DickSwart/smart-fish-tank/assits/images/fish-tank/IMG_0641.jpeg

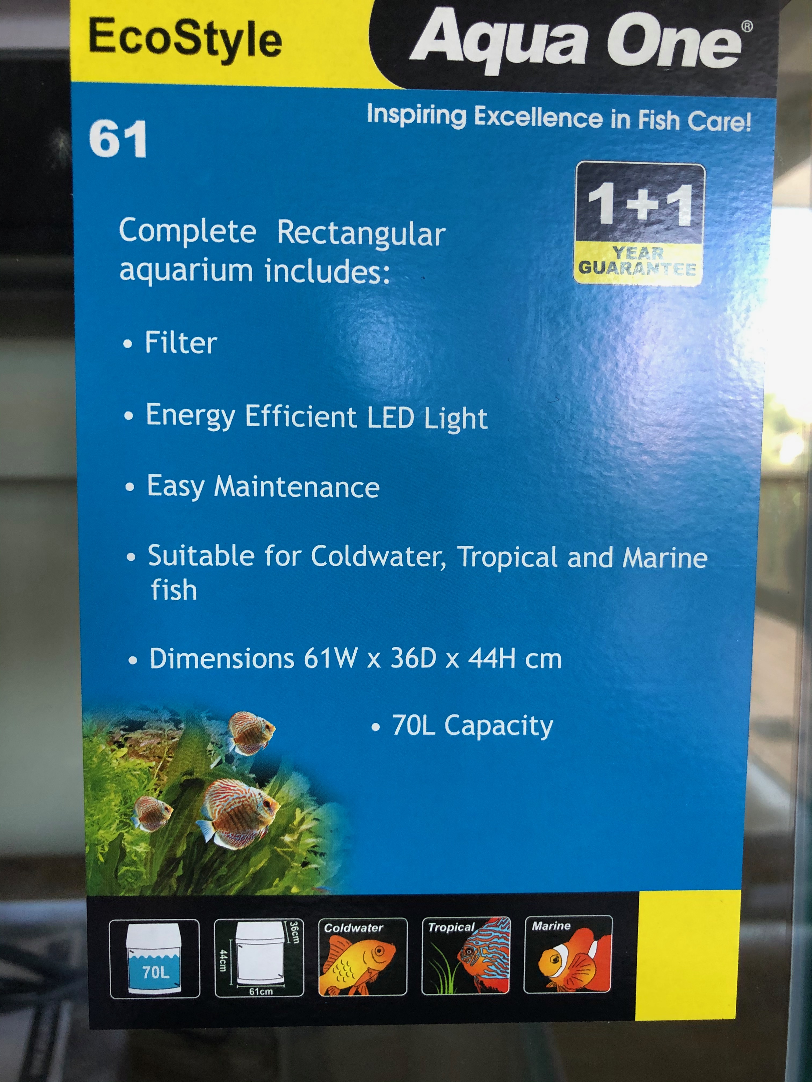
assits/images/fish-tank/IMG_0641.jpeg
