DickSwart/smart-fish-tank/assits/images/fish-tank/IMG_0642.jpeg

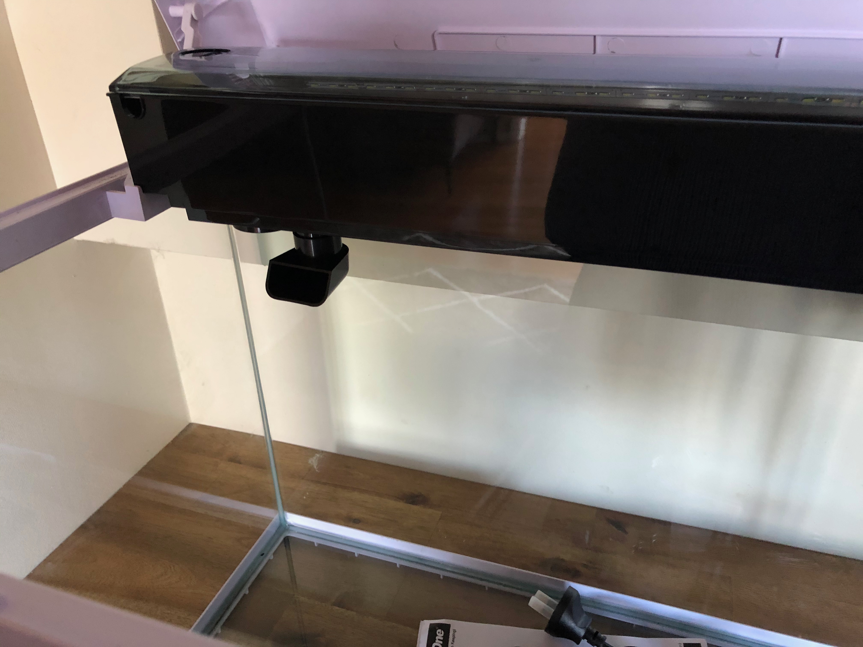
assits/images/fish-tank/IMG_0642.jpeg
