DickSwart/smart-fish-tank/assits/images/fish-tank/IMG_0643.jpeg

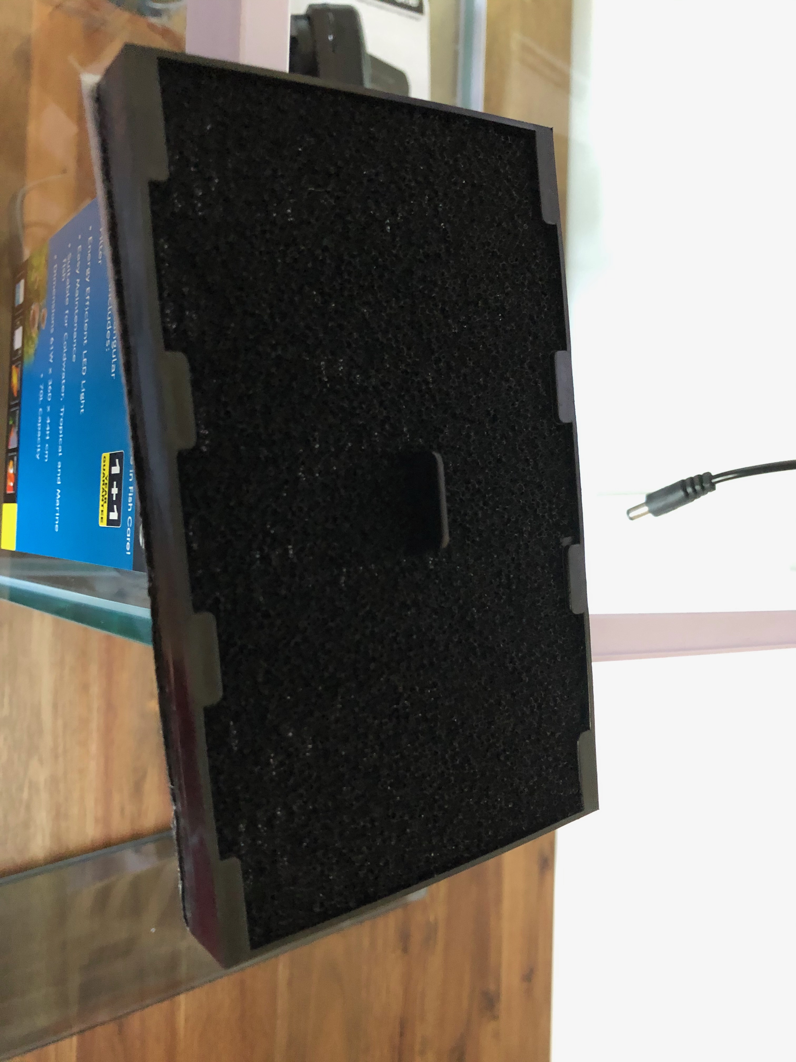
assits/images/fish-tank/IMG_0643.jpeg
