DickSwart/smart-fish-tank/assits/images/fish-tank/IMG_0644.jpeg

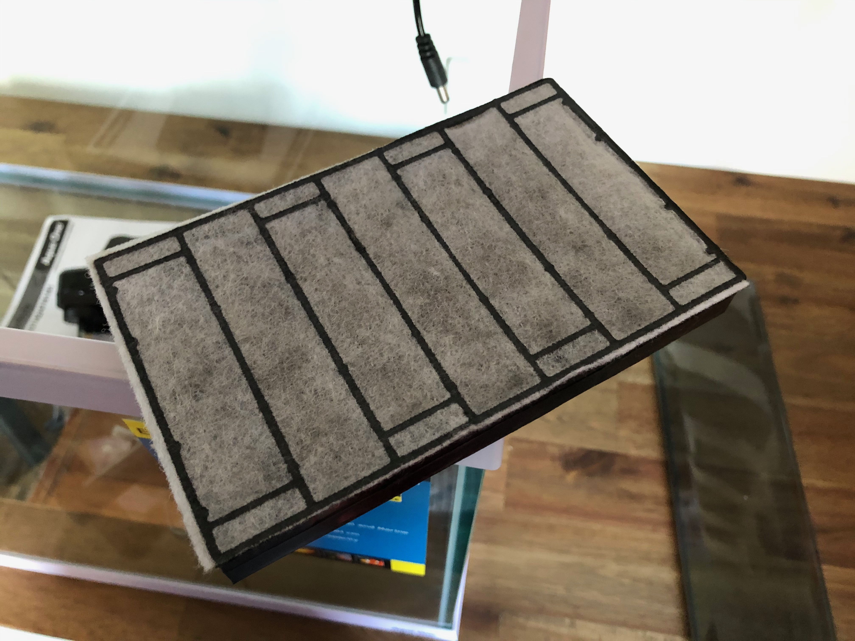
assits/images/fish-tank/IMG_0644.jpeg
