DickSwart/smart-fish-tank/assits/images/fish-tank/IMG_0646.jpeg

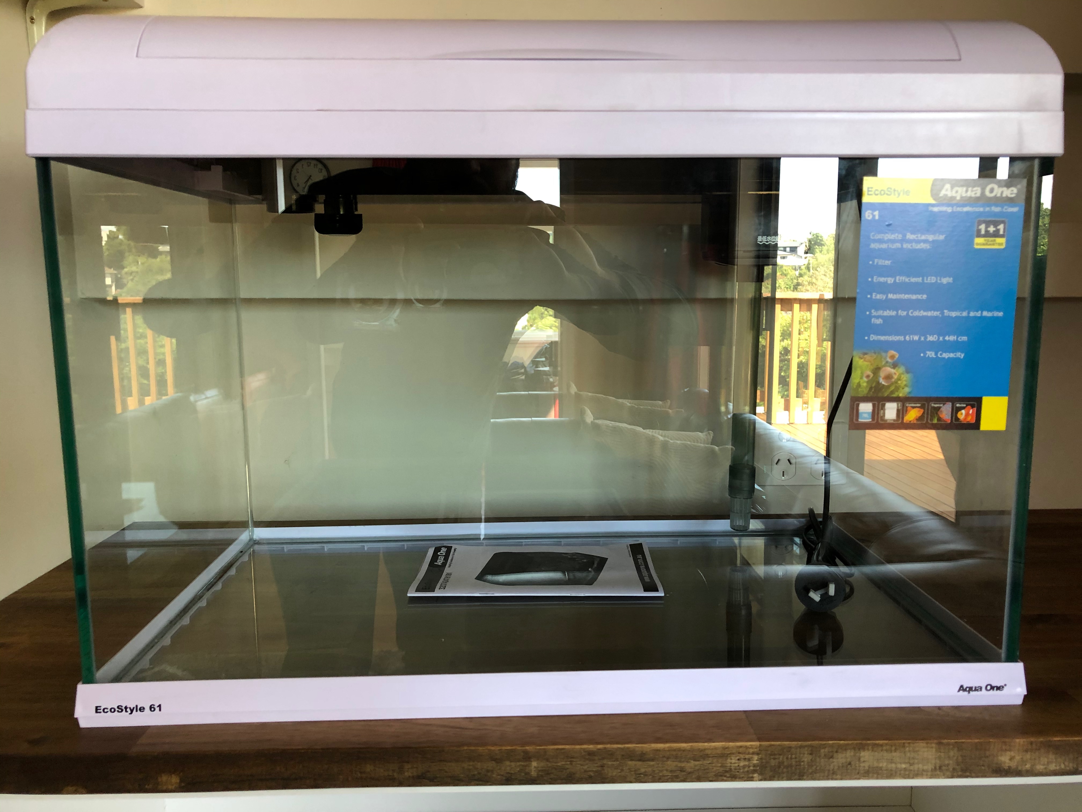
assits/images/fish-tank/IMG_0646.jpeg
