DickSwart/smart-fish-tank/assits/images/fish-tank/IMG_0647.jpeg

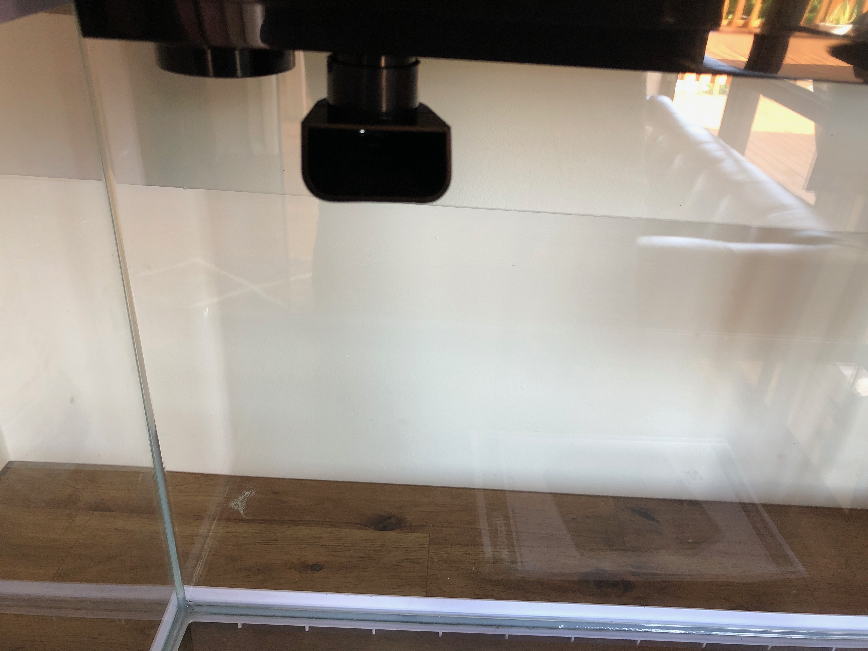
assits/images/fish-tank/IMG_0647.jpeg
