DickSwart/smart-fish-tank/assits/images/fish-tank/IMG_0648.jpeg

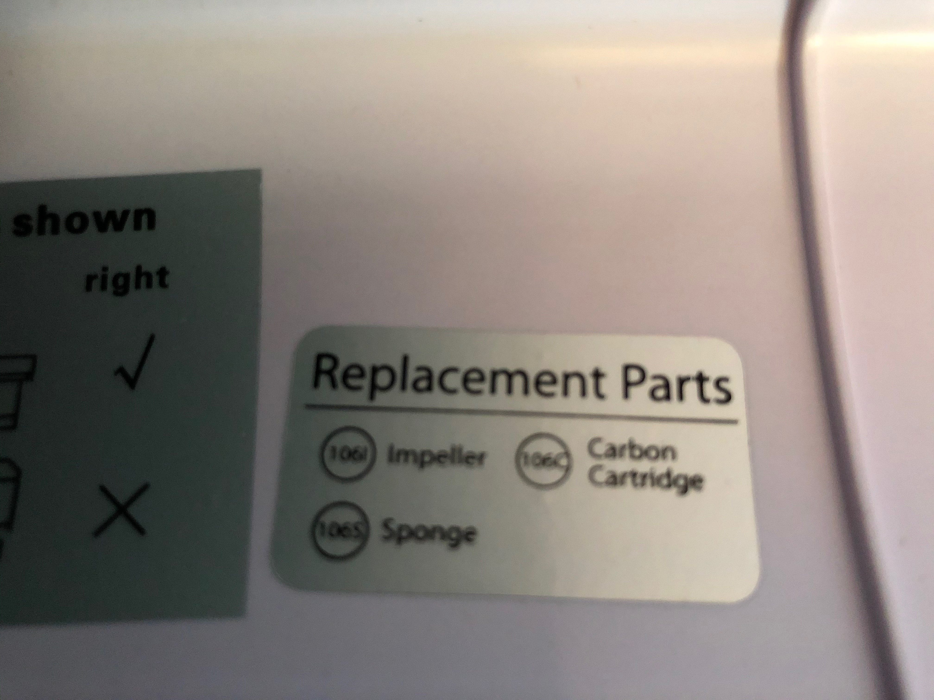
assits/images/fish-tank/IMG_0648.jpeg
