DickSwart/smart-fish-tank/assits/images/project/IMG_0650.jpeg

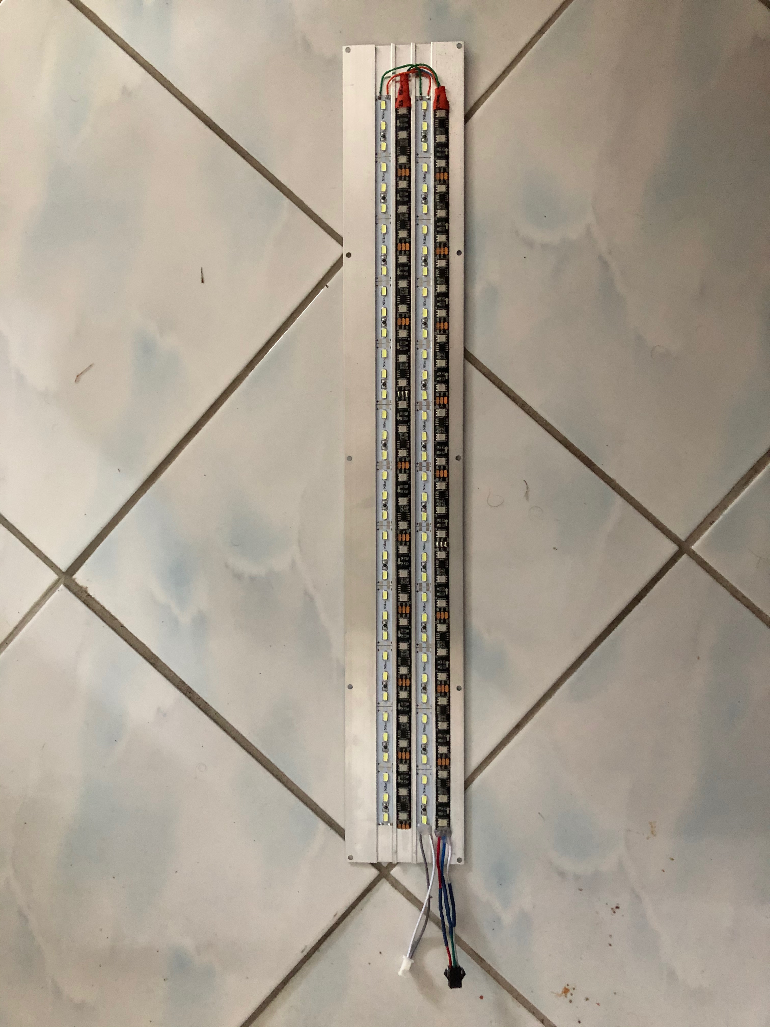
assits/images/project/IMG_0650.jpeg
