DickSwart/smart-fish-tank/assits/images/project/IMG_0651.jpeg

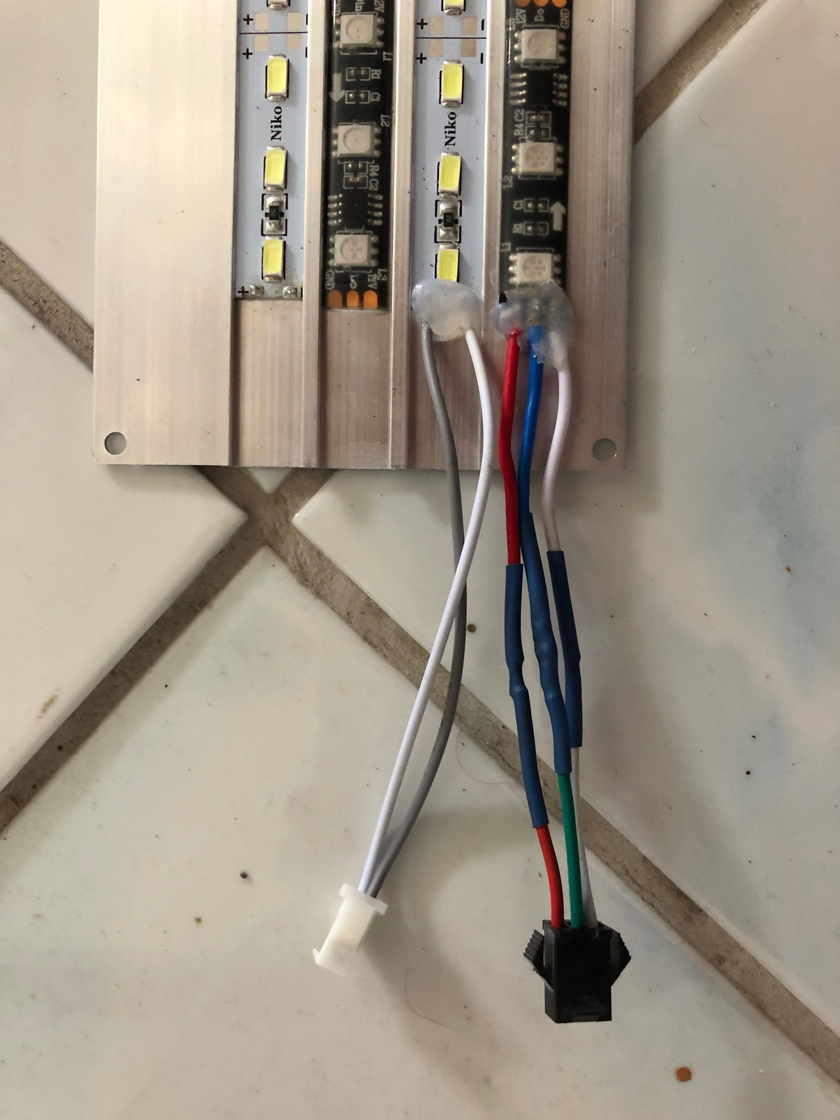
assits/images/project/IMG_0651.jpeg
