DickSwart/smart-fish-tank/assits/images/project/IMG_0652.jpeg

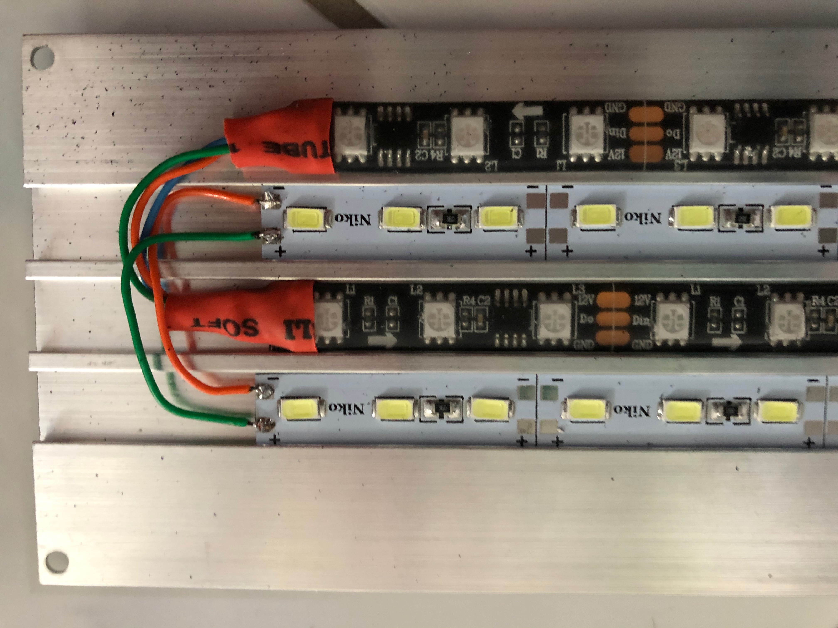
assits/images/project/IMG_0652.jpeg
