DickSwart/smart-fish-tank/assits/images/project/IMG_0653.jpeg

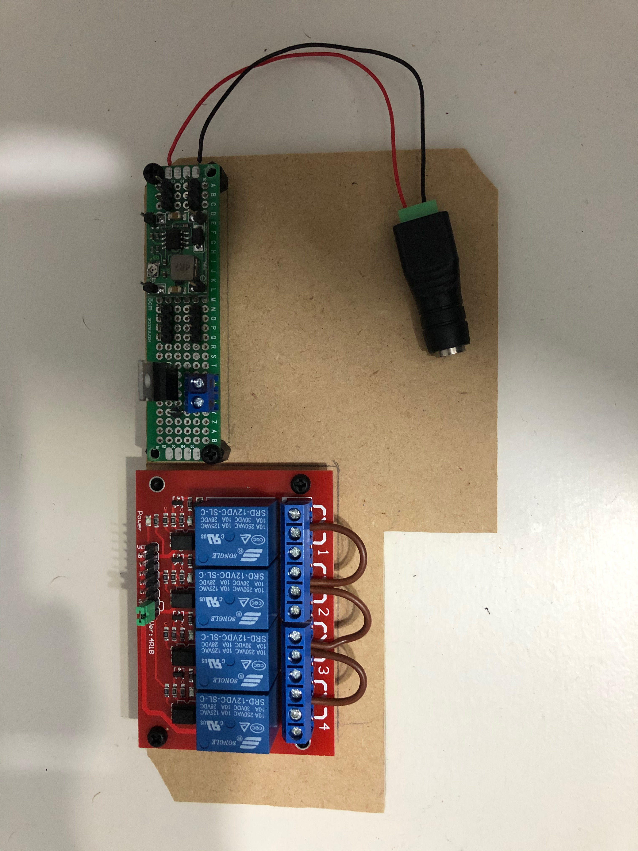
assits/images/project/IMG_0653.jpeg
